ribeirosheila/VoltBridgeADC/imagens/LabView/Captura de tela 2024-11-21 034002.png

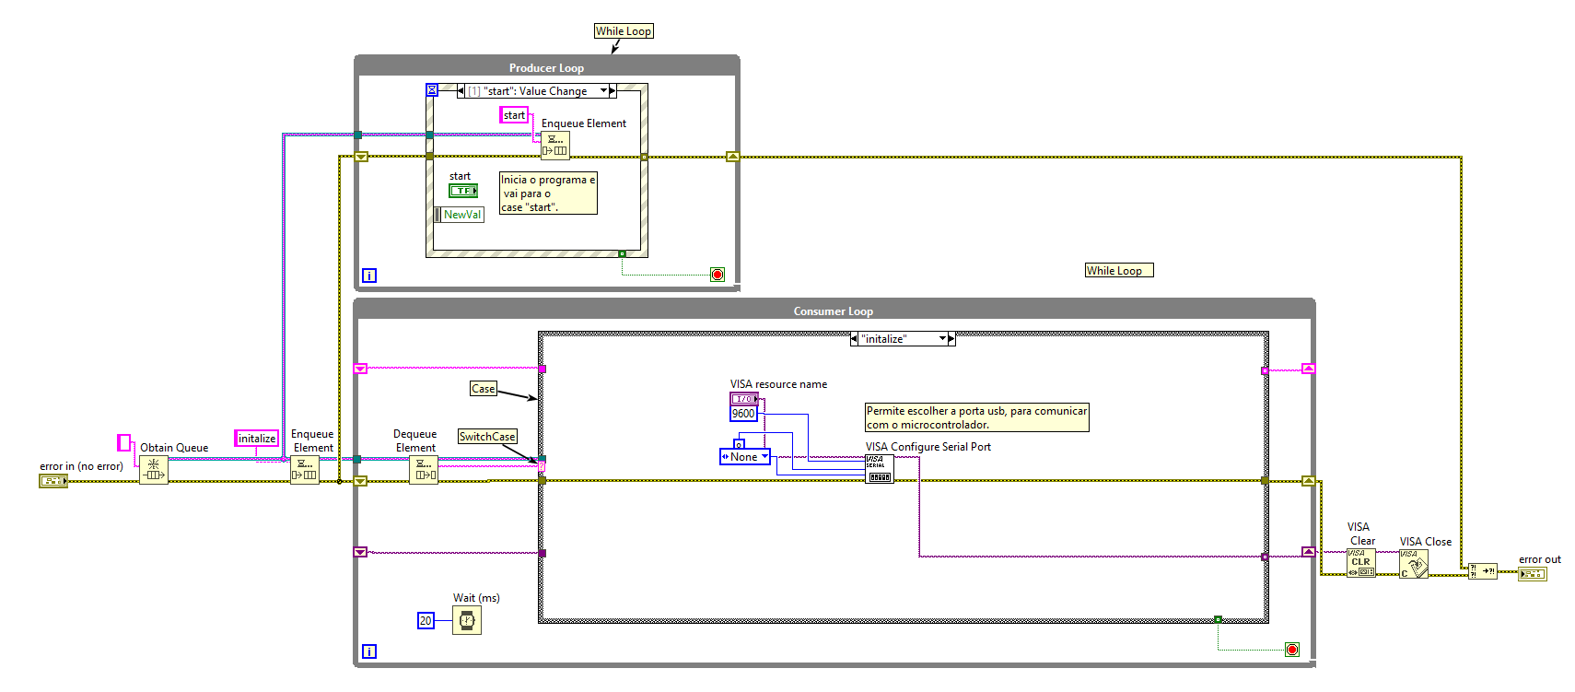
imagens/LabView/Captura de tela 2024-11-21 034002.png
